RubiscoZLesg/Wotagei-Stick/Source/Stick_Controller/IPS/lcdfont.h

#ifndef __LCDFONT_H
#define __LCDFONT_H

const unsigned char ascii_1206[][12] = {
	{0x00, 0x00, 0x00, 0x00, 0x00, 0x00, 0x00, 0x00, 0x00, 0x00, 0x00, 0x00}, /*" ",0*/
	{0x00, 0x00, 0x04, 0x04, 0x04, 0x04, 0x04, 0x00, 0x00, 0x04, 0x00, 0x00}, /*"!",1*/
	{0x14, 0x14, 0x0A, 0x00, 0x00, 0x00, 0x00, 0x00, 0x00, 0x00, 0x00, 0x00}, /*""",2*/
	{0x00, 0x00, 0x0A, 0x0A, 0x1F, 0x0A, 0x0A, 0x1F, 0x0A, 0x0A, 0x00, 0x00}, /*"#",3*/
	{0x00, 0x04, 0x0E, 0x15, 0x05, 0x06, 0x0C, 0x14, 0x15, 0x0E, 0x04, 0x00}, /*"$",4*/
	{0x00, 0x00, 0x12, 0x15, 0x0D, 0x15, 0x2E, 0x2C, 0x2A, 0x12, 0x00, 0x00}, /*"%",5*/
	{0x00, 0x00, 0x04, 0x0A, 0x0A, 0x36, 0x15, 0x15, 0x29, 0x16, 0x00, 0x00}, /*"&",6*/
	{0x02, 0x02, 0x01, 0x00, 0x00, 0x00, 0x00, 0x00, 0x00, 0x00, 0x00, 0x00}, /*"'",7*/
	{0x10, 0x08, 0x08, 0x04, 0x04, 0x04, 0x04, 0x04, 0x08, 0x08, 0x10, 0x00}, /*"(",8*/
	{0x02, 0x04, 0x04, 0x08, 0x08, 0x08, 0x08, 0x08, 0x04, 0x04, 0x02, 0x00}, /*")",9*/
	{0x00, 0x00, 0x00, 0x04, 0x15, 0x0E, 0x0E, 0x15, 0x04, 0x00, 0x00, 0x00}, /*"*",10*/
	{0x00, 0x00, 0x00, 0x08, 0x08, 0x3E, 0x08, 0x08, 0x00, 0x00, 0x00, 0x00}, /*"+",11*/
	{0x00, 0x00, 0x00, 0x00, 0x00, 0x00, 0x00, 0x00, 0x02, 0x02, 0x01, 0x00}, /*",",12*/
	{0x00, 0x00, 0x00, 0x00, 0x00, 0x3F, 0x00, 0x00, 0x00, 0x00, 0x00, 0x00}, /*"-",13*/
	{0x00, 0x00, 0x00, 0x00, 0x00, 0x00, 0x00, 0x00, 0x00, 0x02, 0x00, 0x00}, /*".",14*/
	{0x00, 0x20, 0x10, 0x10, 0x08, 0x08, 0x04, 0x04, 0x02, 0x02, 0x01, 0x00}, /*"/",15*/
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
	{0x00, 0x00, 0x00, 0x00, 0x00, 0x00, 0x00, 0x00, 0x00, 0x00, 0x00, 0x00, 0xC0, 0x13, 0x70, 0x1C, 0x10, 0x10, 0x18, 0x10, 0x0C, 0x20, 0x0C, 0x20, 0x04, 0x00, 0x06, 0x00, 0x06, 0x00, 0x06, 0x00, 0x06, 0x00, 0x06, 0x00, 0x06, 0xFC, 0x06, 0x30, 0x06, 0x30, 0x0C, 0x30, 0x0C, 0x30, 0x18, 0x30, 0x18, 0x30, 0x30, 0x08, 0xC0, 0x07, 0x00, 0x00, 0x00, 0x00, 0x00, 0x00, 0x00, 0x00, 0x00, 0x00}, /*"G",39*/
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
};

#endif
